alvieboy/ZXInterfaceZ/esp32/host/usbh.c

#include "dump.h"
#include "esp_log.h"
#include "defs.h"
#include "os/queue.h"
#include "os/semaphore.h"
#include "os/task.h"
#include "usbh.h"
#include "usb_driver.h"
#include "usb_descriptor.h"
#include <string.h>
#include "log.h"
#include "esp_system.h"
#include "systemevent.h"
#include "usbhub.h"

#define USBHTAG "USBH"
#define USBHDEBUG(x...) LOG_DEBUG(DEBUG_ZONE_USBH, USBHTAG ,x)
#define TAG USBHTAG

static Queue usb_cmd_queue = QUEUE_INIT;
static Queue usb_cplt_queue = QUEUE_INIT;
static Semaphore transaction_sem;

struct usbcmd
{
    int cmd;
    void *data;
};

struct usbresponse
{
    int status;
    int param;
    void *data;
};

static struct usb_hub root_hub = { 0 };

#define USB_CMD_INTERRUPT 0
#define USB_CMD_SUBMITREQUEST 1

#define USB_STAT_ATTACHED_FULLSPEED 1
#define USB_STAT_ATTACHED_LOWSPEED 2
#define USB_REQUEST_COMPLETED_OK 3
#define USB_REQUEST_COMPLETED_FAIL 4




static void usbh__submit_request_to_ll(struct usb_request *req);
static int usbh__control_request_completed_reply(uint8_t chan, uint8_t stat, struct usb_request *req);
static int usbh__request_completed_reply(uint8_t chan, uint8_t stat, void *req);
static int usbh__issue_setup_data_request(struct usb_request *req);

static void usbh__lock_transaction()
{
    if (semaphore__take( transaction_sem,  portMAX_DELAY )!= pdTRUE) {
        ESP_LOGE(TAG, "Cannot take semaphore");
        return;
    }
}

static void usbh__unlock_transaction()
{
    semaphore__give(transaction_sem);
}

void usb_ll__connected_callback(uint8_t fullspeed)
{
    usbh__hub_port_connected(&root_hub, 1, fullspeed?USB_FULL_SPEED:USB_LOW_SPEED);

}
void usbh__hub_port_connected(struct usb_hub *h, int port, usb_speed_t speed)
{
    struct usbresponse resp;

    // Connected device.
    ESP_LOGI(USBHTAG,"USB connection event, speed %s", speed==USB_FULL_SPEED?"FULL":"LOW");
    if (speed == USB_FULL_SPEED)
        resp.status = USB_STAT_ATTACHED_FULLSPEED;
    else
        resp.status = USB_STAT_ATTACHED_LOWSPEED;

    resp.param = port;
    resp.data = h;

    if (queue__send(usb_cplt_queue, &resp, 0)!=OS_TRUE) {
        ESP_LOGE(USBHTAG, "Cannot queue!!!");
    }
}

static void usbh__ll_task(void *pvParam)
{
    struct usbcmd cmd;
    TickType_t tick;
    while (1) {
#ifdef __linux__
        tick = 2;
#else
        tick = portMAX_DELAY;
#endif
        if (queue__receive(usb_cmd_queue, &cmd, tick)==OS_TRUE)
        {
            if (cmd.cmd==USB_CMD_INTERRUPT) {
                usb_ll__interrupt();
            } else {
                // Handle command, pass to low-level if needed.
                if (cmd.cmd==USB_CMD_SUBMITREQUEST) {
                    struct usb_request *req = (struct usb_request*)cmd.data;
                    usbh__submit_request_to_ll(req);
                }
            }
        }
#ifdef __linux__
        usb_ll__idle();
#endif
    }
}


void usb__trigger_interrupt(void)
{
    struct usbcmd cmd;
    cmd.cmd = USB_CMD_INTERRUPT;
    queue__send(usb_cmd_queue, &cmd, OS_MAX_DELAY);
}

static void usbh__reset(void)
{
    usb_ll__reset();

    task__delay_ms(100);
}

char *usbh__string_unicode8_to_char(const uint8_t  *src, unsigned len)
{
    if (len&1) {
        ESP_LOGE(TAG,"String len is odd!");
        return NULL;
    }
    len>>=1;
    char *ret = (char*)malloc(len+1);

    if (ret==NULL)
        return ret;

    char *tptr = ret;

    while (len--) {
        uint8_t a = *src++;
        uint8_t b = *src++;
        if (a==0) {
            *tptr++=b;
        } else {
            *tptr++='?';
        }
    }
    *tptr='\0';
    return ret;
}



int usbh__claim_interface(struct usb_device *dev, struct usb_interface *intf)
{
    if (intf->claimed>0) {
        return -1; // already claimed.
    }
    intf->claimed++;
    dev->claimed++;

    return 0;
}

static void usbh__main_task(void *pvParam)
{
    struct usbresponse resp;

    while (1) {
        USBHDEBUG("Wait for completion responses");
        if (queue__receive(usb_cplt_queue, &resp, OS_MAX_DELAY)==OS_TRUE)
        {
            USBHDEBUG(" >>> got status %d", resp.status);

            struct usb_hub *h = resp.data;

            if (resp.status == USB_STAT_ATTACHED_FULLSPEED) {
                usbhub__port_reset(h, resp.param, USB_FULL_SPEED);
            } else if (resp.status == USB_STAT_ATTACHED_LOWSPEED) {
                usbhub__port_reset(h, resp.param, USB_LOW_SPEED);
            }
        } else {
            ESP_LOGE(USBHTAG, "Queue error!!!");
        }
    }
}

static void usbh__request_completed(struct usb_request *req);
static int usbh__send_ack(struct usb_request *req);


static void usbh__request_failed(struct usb_request *req)
{
    // TODO: resubmit request

    switch (req->control_state) {
    case CONTROL_STATE_SETUP:
        if (req->retries--) {
            req->size_transferred = 0;
            usbh__submit_request_to_ll(req);
            return;
        }
        break;
    case CONTROL_STATE_DATA:
        // Re-issue IN
        if (req->retries--) {
            usbh__issue_setup_data_request(req);
            //usbh__submit_request_to_ll(req);
            return;
        }
        break;
    case CONTROL_STATE_STATUS:
        if (req->retries--) {
            if (req->direction==REQ_DEVICE_TO_HOST) {
                usbh__send_ack(req);
                return;
            }
        }
        break;
    }
    struct usbresponse resp;
    resp.status = USB_REQUEST_COMPLETED_FAIL;
    resp.data = req;
    queue__send(usb_cplt_queue, &resp, OS_MAX_DELAY);
    taskYIELD();
}

static inline int usbh__request_data_remain(const struct usb_request*req, unsigned last_transaction)
{
    // If we got a short packet, then we are done.

    // TODO: ensure this is smaller than EP size
    int remain = req->length - req->size_transferred;
    uint8_t epsize = usb_ll__get_channel_maxsize(req->channel);

    if (remain > epsize) {
        remain = epsize;
    }
    USBHDEBUG("Chan %d: remain %d length req %d transferred %d", req->channel,
              remain,
              req->length,
              req->size_transferred);

    if (remain>0 && (last_transaction < epsize)) {
        USBHDEBUG("Chan %d: Short response (%d epsize %d), returning 0", req->channel,
                  last_transaction, epsize);
        return 0;
    }

    return remain;
}

static int usbh__send_ack(struct usb_request *req)
{
    // Send ack
    usb_ll__set_seq(req->channel, 1);
    return usb_ll__submit_request(req->channel,
                                  PID_OUT,
                                  NULL,
                                  0,
                                  usbh__request_completed_reply,
                                  req);
}

static int usbh__wait_ack(struct usb_request *req)
{
    return usb_ll__submit_request(req->channel,
                                  PID_IN,
                                  NULL,
                                  0,
                                  usbh__request_completed_reply,
                                  req);

}

static int usbh__issue_setup_data_request(struct usb_request *req)
{
    int remain = usbh__request_data_remain(req, usb_ll__get_channel_maxsize(req->channel));

    if (req->direction==REQ_DEVICE_TO_HOST) {
        // send IN request.
        return usb_ll__submit_request(req->channel,
                                      PID_IN,
                                      req->rptr,
                                      remain,
                                      usbh__request_completed_reply,
                                      req);
    } else {
        // send OUT request.
        return usb_ll__submit_request(req->channel,
                                      PID_OUT,
                                      req->rptr,
                                      remain,
                                      usbh__request_completed_reply,
                                      req);
    }
}

/*
 Example transfers:

 H2D, no data phase:
                             SM state
 * -> SETUP                  send, enter CONTROL_STATE_SETUP
 * <- ACK                    Interrupt, send IN request, enter CONTROL_STATE_STATUS
 * -> IN
 * <- DATAX(0len)
 * -> ACK                    Interrupt, completed

 H2D, data phase:

 * -> SETUP                  send, enter CONTROL_STATE_SETUP
 * <- ACK                    Interrupt, send OUT request, enter CONTROL_STATE_DATA
 * -> OUT  ]
 * <- ACK  ] times X         Interrupt, if more send OUT, stay, , else send IN, enter CONTROL_STATE_STATUS
 * -> IN
 * <- DATAX(0len)
 * <- ACK                    Interrupt, completed

 D2H, data phase:

 * -> SETUP                  send, enter CONTROL_STATE_SETUP
 * <- ACK                    Interrupt, send IN request, enter CONTROL_STATE_DATA
 * -> IN  ]
 * <- ACK  ] times X         Interrupt, if more send IN, stay , else send OUT(0), enter CONTROL_STATE_STATUS
 * -> OUT (0len)
 * <- ACK                    Interrupt, completed.

 */


static int usbh__control_request_completed_reply(uint8_t chan, uint8_t stat, struct usb_request *req)
{
    uint8_t rxlen = 0;

    if (stat & 1) {
        // For libusb, all completes immediatly


        switch (req->control_state) {
        case CONTROL_STATE_SETUP:

            /* Setup completed. If we have a data phase, send data */
            req->size_transferred = 0;
            //req->seq = 1;

            if (req->direction==REQ_DEVICE_TO_HOST) {
                usb_ll__read_in_block(chan, req->rptr, &rxlen);
            }
            req->rptr += rxlen;
            req->size_transferred += rxlen;

            usbh__request_completed(req);
        }



    } else {
        ESP_LOGE(USBHTAG, "Request failed 0x%02x",stat);
        usbh__request_failed(req);
        return -1;
    }
    return 0;
}

static int usbh__bulk_request_completed_reply(uint8_t chan, uint8_t stat, struct usb_request *req)
{
    uint8_t rxlen = 0;

    if (stat & 1) {
        req->size_transferred = 0;
        //req->seq = 1;

        if (req->direction==REQ_DEVICE_TO_HOST) {
            ESP_LOGI(USBHTAG, "Copying data to user rptr=%p", req->rptr);
            usb_ll__read_in_block(chan, req->rptr, &rxlen);
        }
        req->rptr += rxlen;
        req->size_transferred += rxlen;

        usbh__request_completed(req);
    } else {
        ESP_LOGE(USBHTAG, "Request failed 0x%02x",stat);
        usbh__request_failed(req);
        return -1;
    }
    return 0;

}
int usbh__request_completed_reply(uint8_t chan, uint8_t stat, void *data)
{
    struct usb_request *req = (struct usb_request*)data;

    if (req->control) {
        return usbh__control_request_completed_reply(chan,stat,req);
    } else {
        return usbh__bulk_request_completed_reply(chan,stat,req);
    }

    return 0;
}

void usbh__submit_request(struct usb_request *req)
{
    struct usbcmd cmd;
    cmd.cmd = USB_CMD_SUBMITREQUEST;
    cmd.data = req;

    usbh__lock_transaction();

    queue__send( usb_cmd_queue, &cmd, OS_MAX_DELAY);
    taskYIELD();
}


static void usbh__submit_request_to_ll(struct usb_request *req)
{
    if (req->control) {
        USBHDEBUG("Submitting CONTROL %p", req);

        usb_ll__set_seq(req->channel, 0);

        usb_ll__submit_request(req->channel,
                               PID_SETUP,
                               req->setup.data,
                               sizeof(req->setup),
                               usbh__request_completed_reply,
                               req);
    } else {
        if (req->direction==REQ_DEVICE_TO_HOST) {
            USBHDEBUG("Submitting BULK IN %p", req);
            usb_ll__submit_request(req->channel,
                                   PID_IN,
                                   req->target,
                                   req->length > 64 ? 64: req->length,
                                   usbh__request_completed_reply,
                                   req);
        } else {
            if (req->length) {
                USBHDEBUG("Submitting BULK OUT %p", req);

                usb_ll__submit_request(req->channel,
                                       PID_OUT,
                                       req->target,
                                       req->length > 64 ? 64: req->length,
                                       usbh__request_completed_reply,
                                       req);
            }
        }

    }
}

int usbh__control_msg(struct usb_device *dev,
                      uint8_t request,
                      uint8_t type,
                      uint16_t value,
                      uint16_t index,
                      uint8_t * data,
                      uint16_t length,
                      int timeout_ticks,
                      unsigned *size_transferred)
{
    struct usb_request req = {0};

    req.device = dev;
    req.target = data;
    req.length = length;
    req.rptr = data;
    req.size_transferred = 0;
    if (type & USB_DEVICE_TO_HOST)
        req.direction = REQ_DEVICE_TO_HOST;
    else
        req.direction = REQ_HOST_TO_DEVICE;

    req.control = 1;
    req.retries = 3;
    req.channel = dev->ep0_chan;

    USBHDEBUG("Control request type %02x", type);

    req.setup.bmRequestType = type;
    req.setup.bRequest = request;
    req.setup.wValue = __le16(value);
    req.setup.wIndex = __le16(index);
    req.setup.wLength = __le16(length);

    usbh__submit_request(&req);

    // Wait.
    if (usbh__wait_completion(&req, timeout_ticks)<0) {
        return -1;
    }

    if (size_transferred)
        *size_transferred = req.size_transferred;

    return 0;
}

int usbh__get_descriptor(struct usb_device *dev,
                         uint8_t  req_type,
                         uint16_t value,
                         uint8_t* target,
                         uint16_t length,
                         uint16_t *size_transferred)
{
    struct usb_request req = {0};

    req.device = dev;
    req.target = target;
    req.length = length;
    req.rptr = target;
    req.size_transferred = 0;
    req.direction = REQ_DEVICE_TO_HOST;
    req.control = 1;
    req.retries = 3;
    req.channel = dev->ep0_chan;
    //req.epsize = dev->ep0_size;


    req.setup.bmRequestType = req_type | USB_DEVICE_TO_HOST;
    req.setup.bRequest = USB_REQ_GET_DESCRIPTOR;
    req.setup.wValue = __le16(value);

    if ((value & 0xff00) == USB_DESC_STRING)
    {
        // Language
        req.setup.wIndex = __le16(0x0409);
    }
    else
    {
        req.setup.wIndex = __le16(0);
    }
    req.setup.wLength = length;
    req.channel =  dev->ep0_chan;
    usbh__submit_request(&req);

    // Wait.
    if (usbh__wait_completion(&req, DESCRIPTOR_FETCH_DEFAULT_TIMEOUT)<0) {
        return -1;
    }
    if (size_transferred)
        *size_transferred = req.size_transferred;

    return 0;
}


void usb_ll__overcurrent_callback()
{
    ESP_LOGE(USBHTAG, "Overcurrent");
    systemevent__send(SYSTEMEVENT_TYPE_USB, SYSTEMEVENT_USB_OVERCURRENT);
}

static void usbh__request_completed(struct usb_request *req)
{
    struct usbresponse resp;
    resp.status = USB_REQUEST_COMPLETED_OK;
    resp.data = req;
    queue__send(usb_cplt_queue, &resp, OS_MAX_DELAY);
    taskYIELD();
}

int usbh__set_configuration(struct usb_device *dev, uint8_t configidx)
{
    struct usb_request req = {0};

    req.device = dev;
    req.target = NULL;
    req.length = 0;
    req.rptr = NULL;
    req.size_transferred = 0;
    req.direction = REQ_HOST_TO_DEVICE;
    req.control = 1;

    req.setup.bmRequestType = USB_REQ_RECIPIENT_DEVICE | USB_REQ_TYPE_STANDARD | USB_HOST_TO_DEVICE;
    req.setup.bRequest = USB_REQ_SET_CONFIGURATION;
    req.setup.wValue = __le16(configidx);
    req.setup.wIndex = __le16(0);
    req.setup.wLength = __le16(0);

    req.channel =  dev->ep0_chan;
    USBHDEBUG("Submitting address request");
    usbh__submit_request(&req);

    // Wait.
    if (usbh__wait_completion(&req, SET_ADDRESS_DEFAULT_TIMEOUT)<0) {
        ESP_LOGE(USBHTAG,"Device not accepting address!");
        return -1;
    }
    USBHDEBUG("Submitted config request");

    return 0;

}

void usbh__dump_info()
{
    usb_ll__dump_info();
}

uint32_t usbh__get_device_id(const struct usb_device*dev)
{
    uint32_t id = dev->device_descriptor.idVendor;
    id<<=16;
    id += dev->device_descriptor.idProduct;
    return id;
}

static int usbh__hub_get_ports(struct usb_hub *h)
{
    return 1;
}

static int usbh__hub_set_power(struct usb_hub *h, int port, int power)
{
    ESP_LOGI(USBHTAG,"Set power, port %d, val=%d\n", port, power);
    if (port==1) {
        usb_ll__set_power(power!=0);
        return 0;
    }
    return -1;
}

static int usbh__hub_reset(struct usb_hub *h, int port)
{
    if (port==1) {
        usbh__reset();
        return 0;
    }
    return -1;
}

int usbh__init()
{
    usb_cmd_queue  = queue__create(4, sizeof(struct usbcmd));
    usb_cplt_queue = queue__create(4, sizeof(struct usbresponse));

    transaction_sem = semaphore__create_mutex();
    if (transaction_sem==NULL) {
        ESP_ERROR_CHECK(-1);
    }

    task__create(usbh__ll_task, "usbh_ll_task", 4096, NULL, 10, NULL);
    task__create(usbh__main_task, "usbh_main_task", 4096, NULL, 11, NULL);

    root_hub.init = NULL;
    root_hub.reset = &usbh__hub_reset;
    root_hub.get_ports = &usbh__hub_get_ports;
    root_hub.set_power = &usbh__hub_set_power;

    usb_ll__init();

    usbhub__new(&root_hub);

    return 0;
}

int usbh__wait_completion(struct usb_request *req, unsigned timeout_ticks)
{
    struct usbresponse resp;
    if (queue__receive(usb_cplt_queue, &resp, timeout_ticks)==OS_TRUE)
    {
        usbh__unlock_transaction();

        USBHDEBUG("USB completed status %d", resp.status);
        if (resp.status == USB_REQUEST_COMPLETED_OK) {
            if (resp.data == req) {
                return 0;
            } else {
                ESP_LOGE(USBHTAG, "NOT FOR US!");
                return -1;
            }
        } else {
            // Error response
            if (resp.data == req) {
                ESP_LOGE(USBHTAG, "Status error!");
               return -1;
            } else {
                ESP_LOGE(USBHTAG, "NOT FOR US!");
                return -1;
            }
       }
    } else {
        usbh__lock_transaction();
    }
    return -1;
}

void usb_ll__disconnected_callback()
{
    ESP_LOGE("USB", "Disconnected callback");
    usbhub__port_disconnect(&root_hub, 1);
}
