alvieboy/ZXInterfaceZ/esp32/main/disassemble_tables.c

#include <inttypes.h>
const char * const disassemble_ops[] = {
"NOP"
,"LD"
,"INC"
,"DEC"
,"RLCA"
,"EX"
,"ADD"
,"RRCA"
,"DJNZ"
,"RLA"
,"JR"
,"RRA"
,"DAA"
,"CPL"
,"SCF"
,"CCF"
,"HALT"
,"ADC"
,"SUB"
,"SBC"
,"AND"
,"XOR"
,"OR"
,"CP"
,"RET"
,"POP"
,"JP"
,"CALL"
,"PUSH"
,"RST"
,"OUT"
,"EXX"
,"IN"
,"DI"
,"EI"
,"RLC"
,"RRC"
,"RL"
,"RR"
,"SLA"
,"SRA"
,"SLL"
,"SRL"
,"BIT"
,"RES"
,"SET"
,"NEG"
,"RETN"
,"IM"
,"RETI"
,"RRD"
,"RLD"
,"LDI"
,"CPI"
,"INI"
,"OUTI"
,"LDD"
,"CPD"
,"IND"
,"OUTD"
,"LDIR"
,"CPIR"
,"INIR"
,"OTIR"
,"LDDR"
,"CPDR"
,"INDR"
,"OTDR"
};
const char *const disassemble_args[] = {
""
,"BC,w"
,"(BC),A"
,"BC"
,"B"
,"B,b"
,"AF,AF'"
,"z,BC"
,"A,(BC)"
,"C"
,"C,b"
,"d"
,"DE,w"
,"(DE),A"
,"DE"
,"D"
,"D,b"
,"z,DE"
,"A,(DE)"
,"E"
,"E,b"
,"NZ,d"
,"z,w"
,"(w),z"
,"z"
,"h"
,"h,b"
,"Z,d"
,"z,hl"
,"z,(w)"
,"l"
,"l,b"
,"NC,d"
,"SP,w"
,"(w),A"
,"SP"
,"(x)"
,"(x),b"
,"C,d"
,"z,SP"
,"A,(w)"
,"A"
,"A,b"
,"B,B"
,"B,C"
,"B,D"
,"B,E"
,"B,h"
,"B,l"
,"B,(x)"
,"B,A"
,"C,B"
,"C,C"
,"C,D"
,"C,E"
,"C,h"
,"C,l"
,"C,(x)"
,"C,A"
,"D,B"
,"D,C"
,"D,D"
,"D,E"
,"D,h"
,"D,l"
,"D,(x)"
,"D,A"
,"E,B"
,"E,C"
,"E,D"
,"E,E"
,"E,h"
,"E,l"
,"E,(x)"
,"E,A"
,"h,B"
,"h,C"
,"h,D"
,"h,E"
,"h,h"
,"h,l"
,"H,(x)"
,"h,A"
,"l,B"
,"l,C"
,"l,D"
,"l,E"
,"l,h"
,"l,l"
,"L,(x)"
,"l,A"
,"(x),B"
,"(x),C"
,"(x),D"
,"(x),E"
,"(x),H"
,"(x),L"
,"(x),A"
,"A,B"
,"A,C"
,"A,D"
,"A,E"
,"A,h"
,"A,l"
,"A,(x)"
,"A,A"
,"NZ"
,"NZ,w"
,"w"
,"00"
,"Z"
,"Z,w"
,"08"
,"NC"
,"NC,w"
,"(b),A"
,"b"
,"10"
,"C,w"
,"A,(b)"
,"18"
,"PO"
,"PO,w"
,"(SP),z"
,"20"
,"PE"
,"(z)"
,"PE,w"
,"DE,z"
,"28"
,"P"
,"AF"
,"P,w"
,"30"
,"M"
,"SP,z"
,"M,w"
,"38"
,"0,B"
,"0,C"
,"0,D"
,"0,E"
,"0,h"
,"0,l"
,"0,(x)"
,"0,A"
,"1,B"
,"1,C"
,"1,D"
,"1,E"
,"1,h"
,"1,l"
,"1,(x)"
,"1,A"
,"2,B"
,"2,C"
,"2,D"
,"2,E"
,"2,h"
,"2,l"
,"2,(x)"
,"2,A"
,"3,B"
,"3,C"
,"3,D"
,"3,E"
,"3,h"
,"3,l"
,"3,(x)"
,"3,A"
,"4,B"
,"4,C"
,"4,D"
,"4,E"
,"4,h"
,"4,l"
,"4,(x)"
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
,"B,(C)"
,"(C),B"
,"(w),BC"
,"0"
,"I,A"
,"C,(C)"
,"(C),C"
,"BC,(w)"
,"R,A"
,"D,(C)"
,"(C),D"
,"(w),DE"
,"1"
,"A,I"
,"E,(C)"
,"(C),E"
,"DE,(w)"
,"2"
,"A,R"
,"h,(C)"
,"(C),h"
,"l,(C)"
,"(C),l"
,"(w),SP"
,"A,(C)"
,"(C),A"
,"SP,(w)"
};
const uint16_t disassemble_tables[3][256]={
{
0x0000, /* 0 00	NOP */
0x0101, /* 1 01	LD      BC,w */
0x0102, /* 2 02	LD      (BC),A */
0x0203, /* 3 03	INC     BC */
0x0204, /* 4 04	INC     B */
0x0304, /* 5 05	DEC     B */
0x0105, /* 6 06	LD      B,b */
0x0400, /* 7 07	RLCA */
0x0506, /* 8 08	EX      AF,AF' */
0x0607, /* 9 09	ADD     z,BC */
0x0108, /* 10 0A	LD      A,(BC) */
0x0303, /* 11 0B	DEC     BC */
0x0209, /* 12 0C	INC     C */
0x0309, /* 13 0D	DEC     C */
0x010a, /* 14 0E	LD      C,b */
0x0700, /* 15 0F	RRCA */
0x080b, /* 16 10	DJNZ    d */
0x010c, /* 17 11	LD      DE,w */
0x010d, /* 18 12	LD      (DE),A */
0x020e, /* 19 13	INC     DE */
0x020f, /* 20 14	INC     D */
0x030f, /* 21 15	DEC     D */
0x0110, /* 22 16	LD      D,b */
0x0900, /* 23 17	RLA */
0x0a0b, /* 24 18	JR      d */
0x0611, /* 25 19	ADD     z,DE */
0x0112, /* 26 1A	LD      A,(DE) */
0x030e, /* 27 1B	DEC     DE */
0x0213, /* 28 1C	INC     E */
0x0313, /* 29 1D	DEC     E */
0x0114, /* 30 1E	LD      E,b */
0x0b00, /* 31 1F	RRA */
0x0a15, /* 32 20	JR      NZ,d */
0x0116, /* 33 21	LD      z,w */
0x0117, /* 34 22	LD      (w),z */
0x0218, /* 35 23	INC     z */
0x0219, /* 36 24	INC     h */
0x0319, /* 37 25	DEC     h */
0x011a, /* 38 26	LD      h,b */
0x0c00, /* 39 27	DAA */
0x0a1b, /* 40 28	JR      Z,d */
0x061c, /* 41 29	ADD     z,hl */
0x011d, /* 42 2A	LD      z,(w) */
0x0318, /* 43 2B	DEC     z */
0x021e, /* 44 2C	INC     l */
0x031e, /* 45 2D	DEC     l */
0x011f, /* 46 2E	LD      l,b */
0x0d00, /* 47 2F	CPL */
0x0a20, /* 48 30	JR      NC,d */
0x0121, /* 49 31	LD      SP,w */
0x0122, /* 50 32	LD      (w),A */
0x0223, /* 51 33	INC     SP */
0x0224, /* 52 34	INC     (x) */
0x0324, /* 53 35	DEC     (x) */
0x0125, /* 54 36	LD      (x),b */
0x0e00, /* 55 37	SCF */
0x0a26, /* 56 38	JR      C,d */
0x0627, /* 57 39	ADD     z,SP */
0x0128, /* 58 3A	LD      A,(w) */
0x0323, /* 59 3B	DEC     SP */
0x0229, /* 60 3C	INC     A */
0x0329, /* 61 3D	DEC     A */
0x012a, /* 62 3E	LD      A,b */
0x0f00, /* 63 3F	CCF */
0x012b, /* 64 40	LD      B,B */
0x012c, /* 65 41	LD      B,C */
0x012d, /* 66 42	LD      B,D */
0x012e, /* 67 43	LD      B,E */
0x012f, /* 68 44	LD      B,h */
0x0130, /* 69 45	LD      B,l */
0x0131, /* 70 46	LD      B,(x) */
0x0132, /* 71 47	LD      B,A */
0x0133, /* 72 48	LD      C,B */
0x0134, /* 73 49	LD      C,C */
0x0135, /* 74 4A	LD      C,D */
0x0136, /* 75 4B	LD      C,E */
0x0137, /* 76 4C	LD      C,h */
0x0138, /* 77 4D	LD      C,l */
0x0139, /* 78 4E	LD      C,(x) */
0x013a, /* 79 4F	LD      C,A */
0x013b, /* 80 50	LD      D,B */
0x013c, /* 81 51	LD      D,C */
0x013d, /* 82 52	LD      D,D */
0x013e, /* 83 53	LD      D,E */
0x013f, /* 84 54	LD      D,h */
0x0140, /* 85 55	LD      D,l */
0x0141, /* 86 56	LD      D,(x) */
0x0142, /* 87 57	LD      D,A */
0x0143, /* 88 58	LD      E,B */
0x0144, /* 89 59	LD      E,C */
0x0145, /* 90 5A	LD      E,D */
0x0146, /* 91 5B	LD      E,E */
0x0147, /* 92 5C	LD      E,h */
0x0148, /* 93 5D	LD      E,l */
0x0149, /* 94 5E	LD      E,(x) */
0x014a, /* 95 5F	LD      E,A */
0x014b, /* 96 60	LD      h,B */
0x014c, /* 97 61	LD      h,C */
0x014d, /* 98 62	LD      h,D */
0x014e, /* 99 63	LD      h,E */
0x014f, /* 100 64	LD      h,h */
0x0150, /* 101 65	LD      h,l */
0x0151, /* 102 66	LD      H,(x) */
0x0152, /* 103 67	LD      h,A */
0x0153, /* 104 68	LD      l,B */
0x0154, /* 105 69	LD      l,C */
0x0155, /* 106 6A	LD      l,D */
0x0156, /* 107 6B	LD      l,E */
0x0157, /* 108 6C	LD      l,h */
0x0158, /* 109 6D	LD      l,l */
0x0159, /* 110 6E	LD      L,(x) */
0x015a, /* 111 6F	LD      l,A */
0x015b, /* 112 70	LD      (x),B */
0x015c, /* 113 71	LD      (x),C */
0x015d, /* 114 72	LD      (x),D */
0x015e, /* 115 73	LD      (x),E */
0x015f, /* 116 74	LD      (x),H */
0x0160, /* 117 75	LD      (x),L */
0x1000, /* 118 76	HALT */
0x0161, /* 119 77	LD      (x),A */
0x0162, /* 120 78	LD      A,B */
0x0163, /* 121 79	LD      A,C */
0x0164, /* 122 7A	LD      A,D */
0x0165, /* 123 7B	LD      A,E */
0x0166, /* 124 7C	LD      A,h */
0x0167, /* 125 7D	LD      A,l */
0x0168, /* 126 7E	LD      A,(x) */
0x0169, /* 127 7F	LD      A,A */
0x0662, /* 128 80	ADD     A,B */
0x0663, /* 129 81	ADD     A,C */
0x0664, /* 130 82	ADD     A,D */
0x0665, /* 131 83	ADD     A,E */
0x0666, /* 132 84	ADD     A,h */
0x0667, /* 133 85	ADD     A,l */
0x0668, /* 134 86	ADD     A,(x) */
0x0669, /* 135 87	ADD     A,A */
0x1162, /* 136 88	ADC     A,B */
0x1163, /* 137 89	ADC     A,C */
0x1164, /* 138 8A	ADC     A,D */
0x1165, /* 139 8B	ADC     A,E */
0x1166, /* 140 8C	ADC     A,h */
0x1167, /* 141 8D	ADC     A,l */
0x1168, /* 142 8E	ADC     A,(x) */
0x1169, /* 143 8F	ADC     A,A */
0x1204, /* 144 90	SUB     B */
0x1209, /* 145 91	SUB     C */
0x120f, /* 146 92	SUB     D */
0x1213, /* 147 93	SUB     E */
0x1219, /* 148 94	SUB     h */
0x121e, /* 149 95	SUB     l */
0x1224, /* 150 96	SUB     (x) */
0x1229, /* 151 97	SUB     A */
0x1362, /* 152 98	SBC     A,B */
0x1363, /* 153 99	SBC     A,C */
0x1364, /* 154 9A	SBC     A,D */
0x1365, /* 155 9B	SBC     A,E */
0x1366, /* 156 9C	SBC     A,h */
0x1367, /* 157 9D	SBC     A,l */
0x1368, /* 158 9E	SBC     A,(x) */
0x1369, /* 159 9F	SBC     A,A */
0x1404, /* 160 A0	AND     B */
0x1409, /* 161 A1	AND     C */
0x140f, /* 162 A2	AND     D */
0x1413, /* 163 A3	AND     E */
0x1419, /* 164 A4	AND     h */
0x141e, /* 165 A5	AND     l */
0x1424, /* 166 A6	AND     (x) */
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
0xFFFF, /* 246 - undefined*/
0xFFFF, /* 247 - undefined*/
0xFFFF, /* 248 - undefined*/
0xFFFF, /* 249 - undefined*/
0xFFFF, /* 250 - undefined*/
0xFFFF, /* 251 - undefined*/
0xFFFF, /* 252 - undefined*/
0xFFFF, /* 253 - undefined*/
0xFFFF, /* 254 - undefined*/
0xFFFF, /* 255 - undefined*/
},
};
