alvieboy/ZXInterfaceZ/esp32/main/config.c

#include "config.h"
#include "esp_partition.h"
#include "esp_spi_flash.h"
#include "esp_log.h"
#include "defs.h"
#include "esp_spiffs.h"

#define TAG "CONFIG"

void config__init()
{
#ifndef __linux__
    esp_vfs_spiffs_conf_t conf = {
      .base_path = "/config",
      .partition_label = "config",
      .max_files = 128,
      .format_if_mount_failed = true
    };
    
    esp_err_t ret = esp_vfs_spiffs_register(&conf);

    if (ret != ESP_OK) {
        if (ret == ESP_FAIL) {
            ESP_LOGE(TAG, "Failed to mount or format filesystem");
        } else if (ret == ESP_ERR_NOT_FOUND) {
            ESP_LOGE(TAG, "Failed to find SPIFFS partition");
        } else {
            ESP_LOGE(TAG, "Failed to initialize SPIFFS (%s)", esp_err_to_name(ret));
        }
        return;
    }
#endif
}
