alvieboy/ZXInterfaceZ/esp32/main/interfacez_rom.c

unsigned char INTZ_ROM[] = {
  0xf3, 0x11, 0xff, 0xff, 0xc3, 0x80, 0x00, 0x00, 0xc3, 0x08, 0x00, 0x00,
  0x00, 0x00, 0x00, 0x00, 0x00, 0x00, 0x00, 0x00, 0x00, 0x00, 0x00, 0x00,
  0x00, 0x00, 0x00, 0x00, 0x00, 0x00, 0x00, 0x00, 0x00, 0x00, 0x00, 0x00,
  0x00, 0x00, 0x00, 0x00, 0x00, 0x00, 0x00, 0x00, 0x00, 0x00, 0x00, 0x00,
  0x00, 0x00, 0x00, 0x00, 0x00, 0x00, 0x00, 0x00, 0x00, 0x00, 0x00, 0x00,
  0x00, 0x00, 0x00, 0x00, 0x00, 0x00, 0x00, 0x00, 0x00, 0x00, 0x00, 0x00,
  0x00, 0x00, 0x00, 0x00, 0x00, 0x00, 0x00, 0x00, 0x00, 0x00, 0x00, 0x00,
  0x00, 0x00, 0x00, 0x00, 0x00, 0x00, 0x00, 0x00, 0x00, 0x00, 0x00, 0x00,
  0x00, 0x00, 0x00, 0x00, 0x00, 0x00, 0xed, 0x45, 0x00, 0x00, 0x00, 0x00,
  0x00, 0x00, 0x00, 0x00, 0x00, 0x00, 0x00, 0x00, 0x00, 0x00, 0x00, 0x00,
  0x00, 0x00, 0x00, 0x00, 0x00, 0x00, 0x00, 0x00, 0x3e, 0x07, 0xd3, 0xfe,
  0x3e, 0x3f, 0xed, 0x47, 0x62, 0x6b, 0x36, 0x02, 0x2b, 0xbc, 0x20, 0xfa,
  0xa7, 0xed, 0x52, 0x19, 0x23, 0x30, 0x06, 0x35, 0x28, 0x03, 0x35, 0x28,
  0xf3, 0x2b, 0x2b, 0xf9, 0x21, 0x00, 0x40, 0x16, 0xbf, 0x06, 0xff, 0xcd,
  0xc4, 0x00, 0x11, 0x00, 0x40, 0x0e, 0x08, 0x06, 0x0b, 0xdb, 0x0b, 0xb7,
  0x20, 0xfb, 0xdb, 0x0d, 0xcd, 0xe1, 0x00, 0x13, 0x10, 0xf3, 0x1b, 0x0d,
  0x20, 0xed, 0x18, 0xfe, 0x21, 0x00, 0x58, 0x16, 0x03, 0x06, 0x00, 0x3e,
  0x38, 0x77, 0x23, 0x10, 0xfc, 0x15, 0x20, 0xf9, 0xc9, 0xfe, 0x0a, 0x30,
  0x04, 0xc6, 0x30, 0x18, 0x19, 0xc6, 0x37, 0x18, 0x15, 0xc5, 0x47, 0xcb,
  0x3f, 0xcb, 0x3f, 0xcb, 0x3f, 0xcb, 0x3f, 0xcd, 0xd5, 0x00, 0x78, 0xe6,
  0x0f, 0xcd, 0xd5, 0x00, 0xc1, 0xc9, 0xd6, 0x20, 0xc5, 0xd5, 0x01, 0x10,
  0x01, 0x26, 0x00, 0x6f, 0x29, 0x29, 0x29, 0x09, 0x06, 0x08, 0x7e, 0x12,
  0x14, 0x23, 0x10, 0xfa, 0xd1, 0x13, 0xc1, 0xc9, 0x00, 0x00, 0x00, 0x00,
  0x00, 0x00, 0x00, 0x00, 0x00, 0x10, 0x10, 0x10, 0x10, 0x00, 0x10, 0x00,
  0x00, 0x24, 0x24, 0x00, 0x00, 0x00, 0x00, 0x00, 0x00, 0x24, 0x7e, 0x24,
  0x24, 0x7e, 0x24, 0x00, 0x00, 0x08, 0x3e, 0x28, 0x3e, 0x0a, 0x3e, 0x08,
  0x00, 0x62, 0x64, 0x08, 0x10, 0x26, 0x46, 0x00, 0x00, 0x10, 0x28, 0x10,
  0x2a, 0x44, 0x3a, 0x00, 0x00, 0x08, 0x10, 0x00, 0x00, 0x00, 0x00, 0x00,
  0x00, 0x04, 0x08, 0x08, 0x08, 0x08, 0x04, 0x00, 0x00, 0x20, 0x10, 0x10,
  0x10, 0x10, 0x20, 0x00, 0x00, 0x00, 0x14, 0x08, 0x3e, 0x08, 0x14, 0x00,
  0x00, 0x00, 0x08, 0x08, 0x3e, 0x08, 0x08, 0x00, 0x00, 0x00, 0x00, 0x00,
  0x00, 0x08, 0x08, 0x10, 0x00, 0x00, 0x00, 0x00, 0x3e, 0x00, 0x00, 0x00,
  0x00, 0x00, 0x00, 0x00, 0x00, 0x18, 0x18, 0x00, 0x00, 0x00, 0x02, 0x04,
  0x08, 0x10, 0x20, 0x00, 0x00, 0x3c, 0x46, 0x4a, 0x52, 0x62, 0x3c, 0x00,
  0x00, 0x18, 0x28, 0x08, 0x08, 0x08, 0x3e, 0x00, 0x00, 0x3c, 0x42, 0x02,
  0x3c, 0x40, 0x7e, 0x00, 0x00, 0x3c, 0x42, 0x0c, 0x02, 0x42, 0x3c, 0x00,
  0x00, 0x08, 0x18, 0x28, 0x48, 0x7e, 0x08, 0x00, 0x00, 0x7e, 0x40, 0x7c,
  0x02, 0x42, 0x3c, 0x00, 0x00, 0x3c, 0x40, 0x7c, 0x42, 0x42, 0x3c, 0x00,
  0x00, 0x7e, 0x02, 0x04, 0x08, 0x10, 0x10, 0x00, 0x00, 0x3c, 0x42, 0x3c,
  0x42, 0x42, 0x3c, 0x00, 0x00, 0x3c, 0x42, 0x42, 0x3e, 0x02, 0x3c, 0x00,
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
};
unsigned int INTZ_ROM_len = 1040;
