alvieboy/ZXInterfaceZ/esp32/main/interfacez_tasks.h

#ifndef __INTERFACEZ_TASKS_H__
#define __INTERFACEZ_TASKS_H__

#include "esp_task.h"

#define INTERFACEZ_TASK_STACK_SIZE_DEFAULT CONFIG_ESP32_PTHREAD_TASK_STACK_SIZE_DEFAULT

#define NETCMD_TASK_STACK_SIZE INTERFACEZ_TASK_STACK_SIZE_DEFAULT
#define NETCMD_TASK_PRIORITY 5

#define VIDEOSTREAMER_TASK_STACK_SIZE INTERFACEZ_TASK_STACK_SIZE_DEFAULT
#define VIDEOSTREAMER_TASK_PRIORITY 10

#define TAPEPLAYER_TASK_STACK_SIZE INTERFACEZ_TASK_STACK_SIZE_DEFAULT
#define TAPEPLAYER_TASK_PRIORITY 10

#define USBH_LL_TASK_STACK_SIZE INTERFACEZ_TASK_STACK_SIZE_DEFAULT
#define USBH_LL_TASK_PRIORITY 10

#define USBH_MAIN_TASK_STACK_SIZE INTERFACEZ_TASK_STACK_SIZE_DEFAULT
#define USBH_MAIN_TASK_PRIORITY 10

#define SPECTCMD_TASK_STACK_SIZE INTERFACEZ_TASK_STACK_SIZE_DEFAULT
#define SPECTCMD_TASK_PRIORITY 11

#define FIRMWAREWS_TASK_STACK_SIZE INTERFACEZ_TASK_STACK_SIZE_DEFAULT
#define FIRMWAREWS_TASK_PRIORITY 11

#endif
